Someone-s-out-there/ProjectCarHAN/uml/sensor/ultrasoon.png

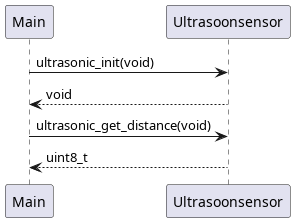
uml/sensor/ultrasoon.png
