Someone-s-out-there/ProjectCarHAN/code/ultrasonic_sensor_test_average/ultrasonic_sensor_test_average.ino

#define trigPin 9
#define echoPin 8

long duration;
int distance;
int refreshRateUS;
int i = 0;

int readings[4];
int average;

constexpr uint8_t FILTER_SHIFT = 4U; // Parameter K
uint16_t
simpleRecursiveFilter(uint16_t filterInput) {
        static uint16_t filterReg; // Delay element - 32 bits

        filterReg = filterReg - (filterReg >> FILTER_SHIFT) + filterInput;
        // Scale output for unity gain.
        return (filterReg >> FILTER_SHIFT);
    }


void setup() {
  Serial.begin(9600);

  // Trigger pin als output en echo pin als input
  pinMode(trigPin, OUTPUT);
  pinMode(echoPin, INPUT);
}

void loop() {
  // Waarom de triggerpin eerst 2 microseconden uit staat is een beetje onduidelijk
  digitalWrite(trigPin, LOW);
  delayMicroseconds(2);

  // Stuurt een geluidsgolf van 10 microseconden lang uit
  digitalWrite(trigPin, HIGH);
  delayMicroseconds(10);
  digitalWrite(trigPin, LOW);

  // Checkt hoelang het duurt voordat de echo pin een input geeft
  duration = pulseIn(echoPin, HIGH);

  // Omrekenen van tijd naar afstand
  distance = duration / 29 / 2;

  
    uint16_t tmp = simpleRecursiveFilter(distance);
    Serial.println(tmp);


  // Print afstand in serial monitor
  // Serial.print("Distance: ");
  // Serial.println(distance);

  // delay(refreshRateUS);

}
